theytookallmynames/HAB/docs/datasheets/gps sensor/info.jpeg

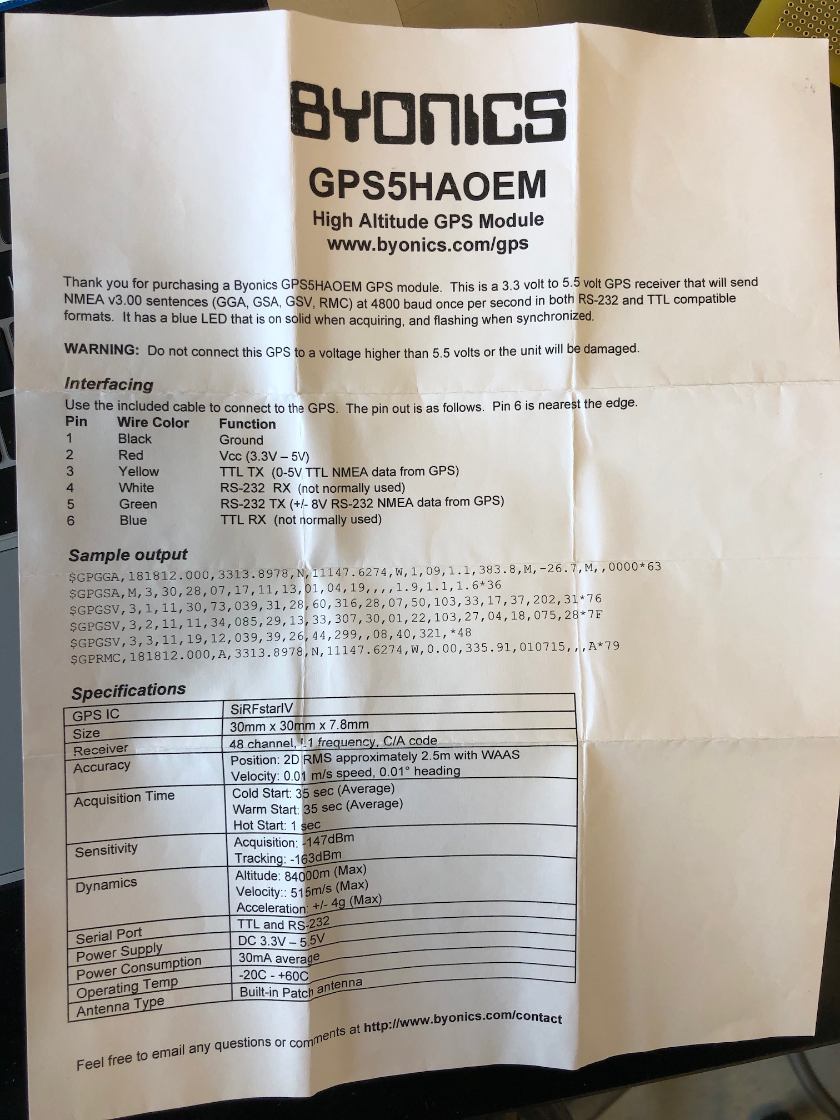
docs/datasheets/gps sensor/info.jpeg
