theytookallmynames/HAB/docs/schematic v2.png

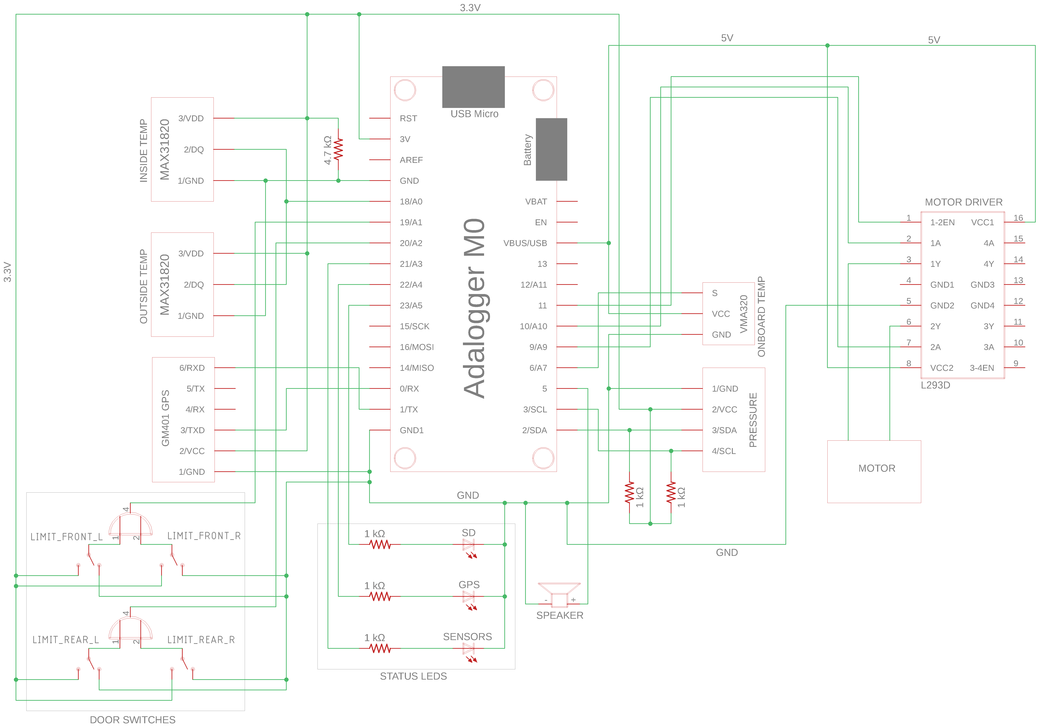
docs/schematic v2.png
