theytookallmynames/HAB/HAB/HAB_Logging.h

#ifndef HAB_LOGGING_H
#define HAB_LOGGING_H
#include "HAB_GPS.h"
#include "HAB_Sensors.h"
#include "HAB_Thermistor.h"
#include "HAB_Door.h"

namespace HAB {
namespace Logging {

class MissionData {
public:
  static String getTitles();
  String toString();
  void setGpsData(GPS::GPSData gpsData);
  void setOnboardTemperature(Sensors::TemperatureData onboardTemperature);
  void setOutdoorTopTemperature(Sensors::TemperatureData outdoorTopTemperature);
  void setOutdoorBottomTemperature(Sensors::TemperatureData outdoorBottomTemperature);
  void setPressureData(Sensors::PressureData pressure);
  void setDoor1Status(Door::DoorStatus door1status);
  void setDoor2Status(Door::DoorStatus door2status);

  // missionData
  typedef struct {
    GPS::GPSData gpsData;
    Sensors::TemperatureData onboardTemperature;
    Sensors::TemperatureData outdoorTopTemperature;
    Sensors::TemperatureData outdoorBottomTemperature;
    Sensors::PressureData pressure;
    Door::DoorStatus door1Status;
    Door::DoorStatus door2Status;
  } Data;

 private:
  Data data;
};

bool init();
void logMissionData(String data);
void logSystemData(String data);

} // namespace Logging
} // namespace HAB

#endif // HAB_LOGGING_H
